MATTMCCA/STM32L071KB-Breakout/IMG/001.png

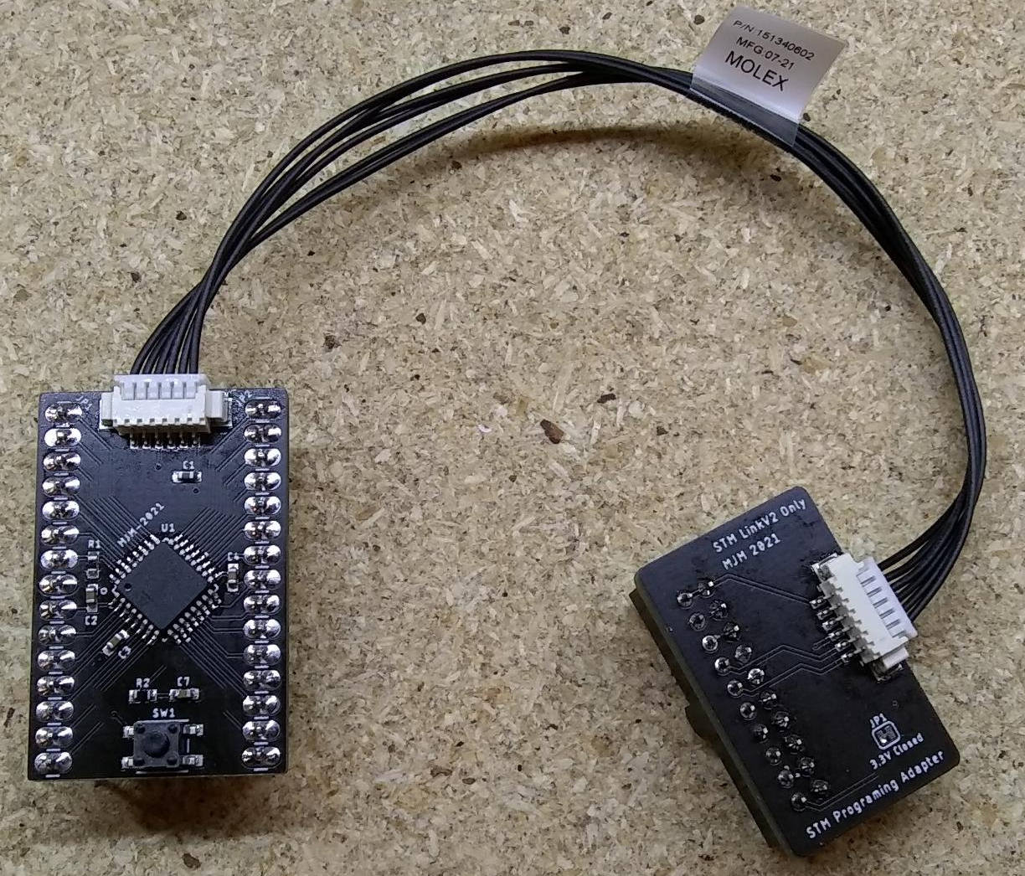
IMG/001.png
