MATTMCCA/STM32L071KB-Breakout/IMG/002.png

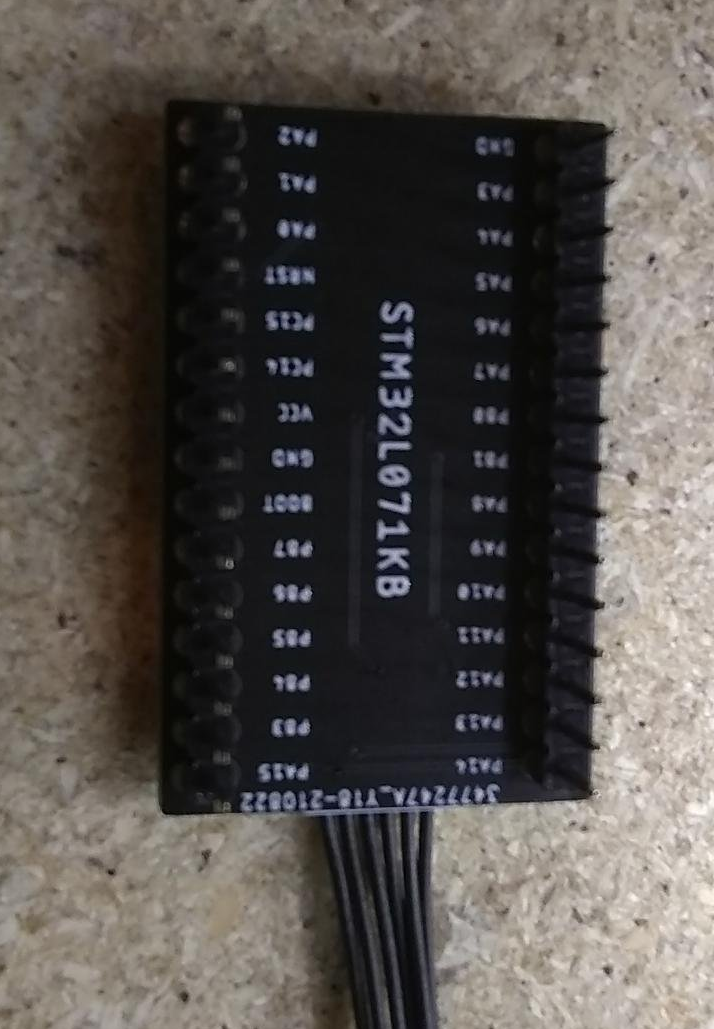
IMG/002.png
