MATTMCCA/STM32L071KB-Breakout/IMG/003.png

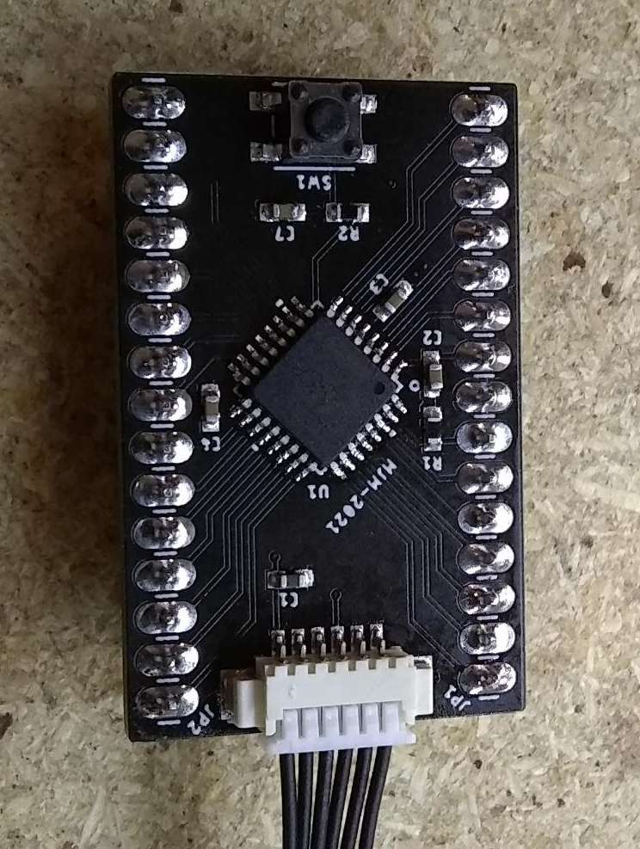
IMG/003.png
