MATTMCCA/STM32L071KB-Breakout/IMG/004.png

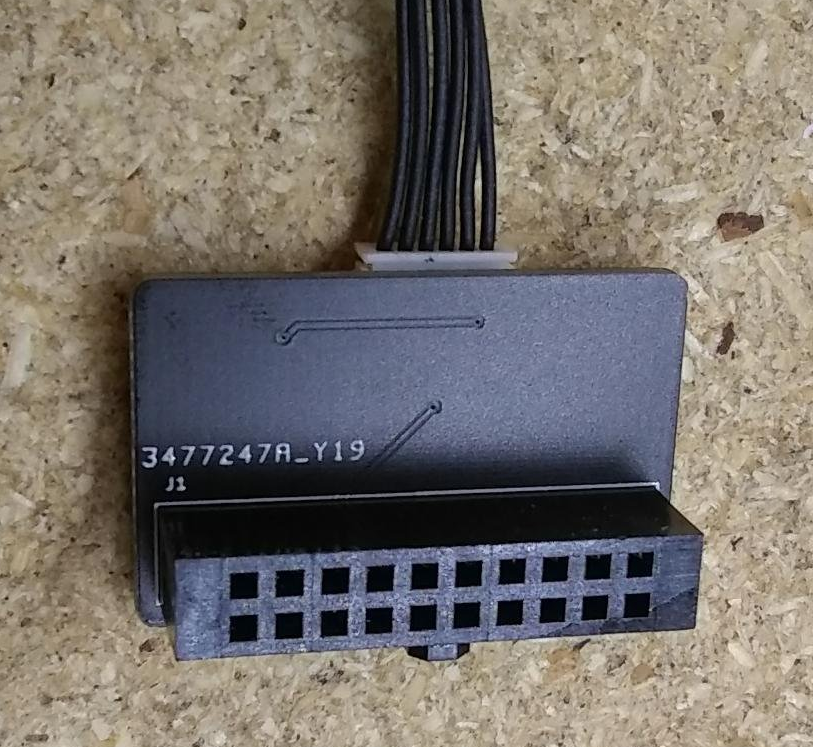
IMG/004.png
