MATTMCCA/STM32L071KB-Breakout/IMG/005.png

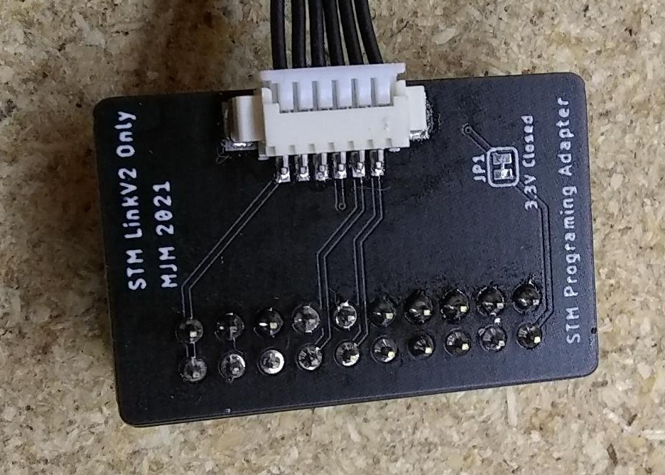
IMG/005.png
